NotaScout/ENGR342/Picture/IMG_0955.jpg

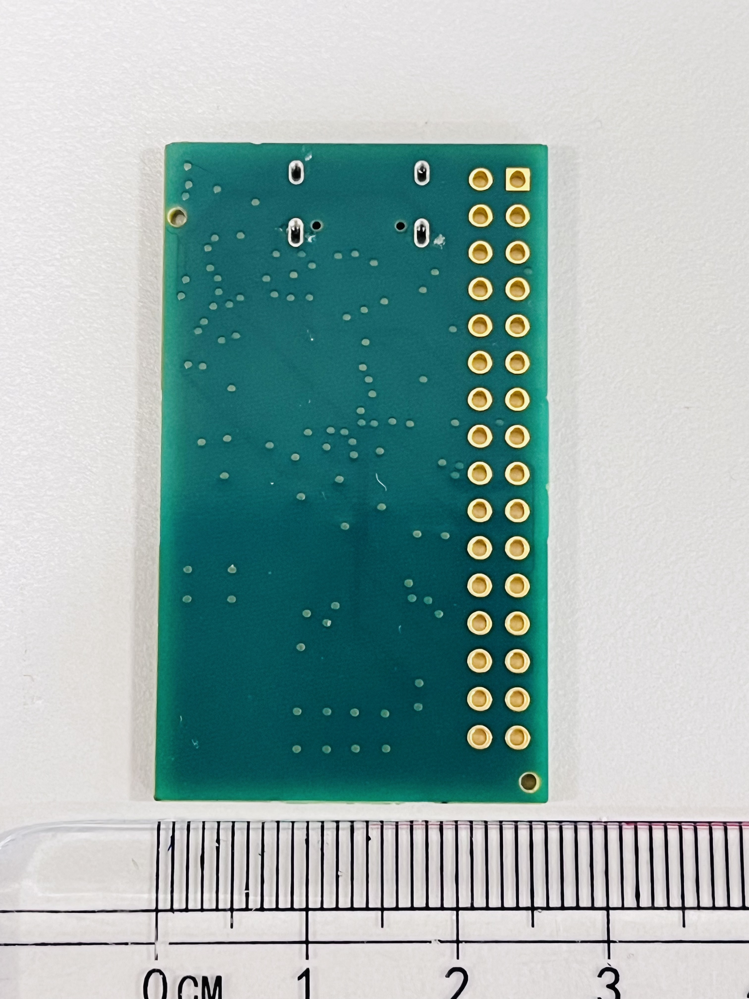
Picture/IMG_0955.jpg
